simonzhou0372/CHUNITHM_TOF_PICO/src/config.cpp

/*
 * Configuration Implementation
 *
 * 修复说明:
 * 1. 增加 config_init() 启动时的详细日志
 * 2. 增加 config_save() 返回 bool 表示成功/失败
 * 3. 增加 Flash 加载后的参数验证日志
 * 4. 保持与现有代码的兼容性
 */

#include "config.h"
#include "save.h"
#include "mpr121.h"  // 引入 MPR121 默认阈值定义
#include <string.h>
#include <stdio.h>
// 注意: log_output.h 必须在所有 SDK/系统头之后 (见 mpr121.cpp 同名注释)
#include "log_output.h"   // printf 总开关 (默认禁用, 只发送 HID 报文)

namespace Chuni245Tof {

//==============================================================================
// 默认配置
//==============================================================================

// Default configuration - Keyboard mode only
static const config_t default_config = {
    .hid_mode = HID_MODE_KEYBOARD_ONLY,  // Default: Keyboard only
    .touch_threshold = MPR121_DEFAULT_TOUCH_THRESHOLD,      // 由 mpr121.h 定义
    .release_threshold = MPR121_DEFAULT_RELEASE_THRESHOLD,  // 由 mpr121.h 定义
    .tof_offset = 120,                    // Default: 120mm 起始高度
    .tof_pitch = 30,                      // Default: 30mm step height for AIR1~AIR11
    .air12_range = 150,                   // Default: 150mm range for AIR12 (更大的范围)
    .air_min_hold_ms = 100,               // Default: 100ms 最小按下持续时间
    .air_overlay_enabled = 1,             // Default: Overlay ON (扩展到 AIR12)
    .air_threshold = {1500, 1500, 1500, 1500, 1500},
};

//==============================================================================
// 全局配置数据
//==============================================================================

config_t* cfg = nullptr;
static config_t config_data;

// Barrier mode (determined at startup, affects default thresholds)
static uint8_t current_barrier_mode = 2;  // Default: mode 2

//==============================================================================
// 配置验证
//==============================================================================

/**
 * 验证配置参数范围
 * @param cfg 配置指针
 * @return 是否需要修正
 */
static bool validate_config(config_t* cfg) {
    bool modified = false;

    // HID 模式验证
    if (cfg->hid_mode > HID_MODE_GAMEPAD_KEYBOARD) {
        printf("CONFIG VALIDATE: hid_mode %d -> %d (invalid)\r\n",
               cfg->hid_mode, default_config.hid_mode);
        cfg->hid_mode = default_config.hid_mode;
        modified = true;
    }

    // MPR121 阈值范围: 已解除限制，允许调试
    // touch_threshold 和 release_threshold 的合理范围需要用户自行把握
    // 注意：touch_threshold 必须大于 release_threshold（迟滞区）
    if (cfg->touch_threshold < 1 || cfg->touch_threshold > 255) {
        printf("CONFIG VALIDATE: touch_threshold %d -> %d (out of range 1-255)\r\n",
               cfg->touch_threshold, default_config.touch_threshold);
        cfg->touch_threshold = default_config.touch_threshold;
        modified = true;
    }
    if (cfg->release_threshold < 1 || cfg->release_threshold > 255) {
        printf("CONFIG VALIDATE: release_threshold %d -> %d (out of range 1-255)\r\n",
               cfg->release_threshold, default_config.release_threshold);
        cfg->release_threshold = default_config.release_threshold;
        modified = true;
    }

    // TOF 参数验证
    if (cfg->tof_offset < 40 || cfg->tof_offset > 200) {
        printf("CONFIG VALIDATE: tof_offset %d -> %d (out of range 40-200)\r\n",
               cfg->tof_offset, default_config.tof_offset);
        cfg->tof_offset = default_config.tof_offset;
        modified = true;
    }
    if (cfg->tof_pitch < 4 || cfg->tof_pitch > 100) {
        printf("CONFIG VALIDATE: tof_pitch %d -> %d (out of range 4-100)\r\n",
               cfg->tof_pitch, default_config.tof_pitch);
        cfg->tof_pitch = default_config.tof_pitch;
        modified = true;
    }

    // Air12 范围验证：必须 >= pitch
    if (cfg->air12_range < cfg->tof_pitch || cfg->air12_range > 255) {
        printf("CONFIG VALIDATE: air12_range %d -> %d (must be >= pitch %d and <= 255)\r\n",
               cfg->air12_range, default_config.air12_range, cfg->tof_pitch);
        cfg->air12_range = default_config.air12_range;
        modified = true;
    }

    // AIR 最小按下时间验证：10-500ms
    if (cfg->air_min_hold_ms < 10 || cfg->air_min_hold_ms > 500) {
        printf("CONFIG VALIDATE: air_min_hold_ms %d -> %d (out of range 10-500)\r\n",
               cfg->air_min_hold_ms, default_config.air_min_hold_ms);
        cfg->air_min_hold_ms = default_config.air_min_hold_ms;
        modified = true;
    }

    // AIR Overlay 模式验证: 0 或 1
    if (cfg->air_overlay_enabled > 1) {
        printf("CONFIG VALIDATE: air_overlay_enabled %d -> %d (invalid, must be 0 or 1)\r\n",
               cfg->air_overlay_enabled, default_config.air_overlay_enabled);
        cfg->air_overlay_enabled = default_config.air_overlay_enabled;
        modified = true;
    }

    return modified;
}

//==============================================================================
// API 实现
//==============================================================================

/**
 * 设置 barrier mode (在 main.cpp 启动时调用)
 * 影响默认 touch/release 阈值
 */
void config_set_barrier_mode(uint8_t mode) {
    current_barrier_mode = mode;
    printf("CONFIG: Barrier mode set to %d\n", mode);
}

/**
 * 获取当前 barrier mode
 */
uint8_t config_get_barrier_mode() {
    return current_barrier_mode;
}

/**
 * 根据 barrier mode 获取默认 touch 阈值
 */
static uint8_t get_default_touch_threshold() {
    switch (current_barrier_mode) {
        case 0: return 20;  // Mode 0: Direct contact
        case 1: return 3;   // Mode 1: Object barrier
        case 2: return 3;   // Mode 2: Object barrier + glove
        default: return 20;
    }
}

/**
 * 根据 barrier mode 获取默认 release 阈值
 */
static uint8_t get_default_release_threshold() {
    switch (current_barrier_mode) {
        case 0: return 18;  // Mode 0: Direct contact
        case 1: return 2;   // Mode 1: Object barrier
        case 2: return 2;   // Mode 2: Object barrier + glove
        default: return 18;
    }
}

/**
 * 初始化配置
 *
 * 流程:
 * 1. 尝试从 Flash 加载
 * 2. 如果加载失败，使用默认配置
 * 3. 验证参数范围
 * 4. 设置全局指针
 */
void config_init() {
    printf("\r\n========================================\r\n");
    printf("CONFIG INIT: Starting configuration load\r\n");
    printf("========================================\r\n");

    // 尝试从 Flash 加载
    bool loaded = save_load(&config_data, sizeof(config_data));

    if (loaded) {
        printf("CONFIG INIT: Loaded from Flash, validating...\r\n");

        // 验证参数范围
        bool modified = validate_config(&config_data);

        if (modified) {
            printf("CONFIG INIT: Parameters corrected after validation\r\n");
        }

        printf("CONFIG LOAD FLASH: touch=%d release=%d offset=%d pitch=%d air12=%d hold=%d overlay=%d\r\n",
               config_data.touch_threshold, config_data.release_threshold,
               config_data.tof_offset, config_data.tof_pitch,
               config_data.air12_range, config_data.air_min_hold_ms, config_data.air_overlay_enabled);
    } else {
        printf("CONFIG INIT: Flash load failed, using defaults\r\n");
        memcpy(&config_data, &default_config, sizeof(config_data));

        // 根据 runtime barrier mode 设置默认阈值
        config_data.touch_threshold = get_default_touch_threshold();
        config_data.release_threshold = get_default_release_threshold();

        printf("CONFIG LOAD DEFAULT: touch=%d release=%d offset=%d pitch=%d air12=%d hold=%d overlay=%d\r\n",
               config_data.touch_threshold, config_data.release_threshold,
               config_data.tof_offset, config_data.tof_pitch,
               config_data.air12_range, config_data.air_min_hold_ms, config_data.air_overlay_enabled);
    }

    // 设置全局指针
    cfg = &config_data;

    printf("========================================\r\n\r\n");
}

/**
 * 保存当前配置到 Flash
 *
 * @return true 保存成功, false 失败
 */
bool config_save() {
    if (!cfg) {
        printf("CONFIG SAVE: ERROR - config not initialized\r\n");
        return false;
    }

    printf("CONFIG SAVE: Saving current config to Flash...\r\n");
    printf("CONFIG SAVE: touch=%d release=%d offset=%d pitch=%d air12=%d hold=%d overlay=%d\r\n",
           cfg->touch_threshold, cfg->release_threshold,
           cfg->tof_offset, cfg->tof_pitch,
           cfg->air12_range, cfg->air_min_hold_ms, cfg->air_overlay_enabled);

    // 延迟保存: 快照后由 save_loop() 在主循环独立节拍执行 Flash 擦写,
    // 避免 CDC 命令路径直接擦写 Flash 造成实时 HID 长时间停顿
    bool success = save_request_write(cfg, sizeof(config_t));

    if (success) {
        printf("CONFIG SAVE: QUEUED (executes on next main loop)\r\n");
    } else {
        printf("CONFIG SAVE: FAILED to queue\r\n");
    }

    return success;
}

/**
 * 重置配置为默认值并保存
 */
void config_reset() {
    if (!cfg) {
        printf("CONFIG RESET: ERROR - config not initialized\r\n");
        return;
    }

    printf("CONFIG RESET: Resetting to defaults...\r\n");
    memcpy(cfg, &default_config, sizeof(config_t));

    if (config_save()) {
        printf("CONFIG RESET: SUCCESS\r\n");
    } else {
        printf("CONFIG RESET: FAILED to save\r\n");
    }
}

} // namespace Chuni245Tof
