simonzhou0372/CHUNITHM_TOF_PICO/src/save.cpp

/*
 * Flash Save Implementation
 *
 * 修复说明:
 * 1. 修正 Flash 地址计算 - 使用 PICO_FLASH_SIZE_BYTES 而不是硬编码 256KB
 * 2. 增加 CRC32 校验确保数据完整性
 * 3. 增加版本号支持未来配置结构变更
 * 4. 增加写入后验证确保数据正确保存
 * 5. 增加详细的调试日志
 */

#include "save.h"
#include "tof_reader.h"
#include "hardware/flash.h"
#include "pico/mutex.h"
#include "pico/time.h"
#include "pico/flash.h"     // flash_safe_execute: SDK 官方双核 Flash 安全机制
#include <string.h>
#include <stdio.h>
// 注意: log_output.h 必须在所有 SDK/系统头之后 (见 mpr121.cpp 同名注释)
#include "log_output.h"     // printf 总开关 (默认禁用, 只发送 HID 报文)

namespace Chuni245Tof {

//==============================================================================
// Flash 配置
//==============================================================================

// 使用 Flash 最后一个 sector 用于存储配置
// RP2040 Pico 默认 Flash 大小为 2MB (PICO_FLASH_SIZE_BYTES)
// 确保不覆盖程序代码区域
#define CONFIG_FLASH_OFFSET (PICO_FLASH_SIZE_BYTES - FLASH_SECTOR_SIZE)
#define CONFIG_FLASH_ADDR (XIP_BASE + CONFIG_FLASH_OFFSET)

// 配置版本号 - 如果将来 config_t 结构改变，需要增加版本号
#define CONFIG_VERSION 1

//==============================================================================
// 持久化配置结构 (写入 Flash 的格式)
//==============================================================================

typedef struct {
    uint32_t magic;        // Magic number 验证
    uint16_t version;      // 配置版本号
    uint16_t reserved;     // 保留字段（对齐）

    // 配置数据（与 config_t 结构一致）
    uint8_t hid_mode;
    uint8_t touch_threshold;
    uint8_t release_threshold;
    uint8_t tof_offset;
    uint8_t tof_pitch;
    uint8_t air12_range;         // AIR12 特殊检测范围（原 air6_range）
    uint16_t air_min_hold_ms;
    uint8_t air_overlay_enabled; // AIR Overlay Mode (0=OFF, 1=ON)
    uint16_t air_threshold[5];

    uint32_t crc32;        // CRC32 校验
} PersistentConfig;

// 确保结构体大小是 Flash Page 大小的整数倍或更小
static_assert(sizeof(PersistentConfig) <= FLASH_PAGE_SIZE,
              "PersistentConfig too large for Flash page");

//==============================================================================
// CRC32 计算
//==============================================================================

// CRC32 查找表 (IEEE 802.3 标准多项式)
static const uint32_t crc32_table[256] = {
    0x00000000, 0x77073096, 0xEE0E612C, 0x990951BA, 0x076DC419, 0x706AF48F,
    0xE963A535, 0x9E6495A3, 0x0EDB8832, 0x79DCB8A4, 0xE0D5E91E, 0x97D2D988,
    0x09B64C2B, 0x7EB17CBD, 0xE7B82D07, 0x90BF1D91, 0x1DBAD10D, 0x6CABE844,
    0xF856B086, 0x8A1D1A5E, 0xE4D65E39, 0x97D2D9D8, 0x05B6B4A1, 0x7A4D3D6C,
    0x04DB2615, 0x73DC1683, 0xE3630B12, 0x94643B84, 0x0D6D6A3E, 0x7A6A5AA8,
    0xE40ECF0B, 0x9309FF9D, 0x0A00AE27, 0x7D079EB1, 0xF00F9344, 0x8708A3D2,
    0x1E01F268, 0x6906C2FE, 0xF762575D, 0x806567CB, 0x196C3671, 0x6E6B06E7,
    0xFED41B76, 0x89D32BE0, 0x10DA7A5A, 0x67DD4ACC, 0xF9B9DF4F, 0x8EBEEFF9,
    0x17B7BE43, 0x60B08ED5, 0xD6D6A3E8, 0xA1D1937E, 0x38D8C2C4, 0x4FDFF252,
    0xD1BB67F1, 0xA6BC5767, 0x3FB506DD, 0x48B2364B, 0xD80D2BDA, 0xAF0A1B4C,
    0x36034AF6, 0x41047A60, 0xDF60EFC3, 0xA867DF55, 0x316E8EEF, 0x4669BE79,
    0xCB61B38C, 0xBC66831A, 0x256FD2A0, 0x5268E236, 0xCC0C7795, 0xBB0B4703,
    0x220216B9, 0x5505262F, 0xC5BA3BBE, 0xB2BD0B28, 0x2BB45A92, 0x5CB36A04,
    0xC2D7FFA7, 0xB5D0CF31, 0x2CD99E8B, 0x5BDEAE1D, 0x9B64C2B0, 0xEC63F22A,
    0x756AA39C, 0x026D930A, 0x9C0906A9, 0xEB0E363F, 0x72076785, 0x05005713,
    0x95BF4A82, 0xE2B87A14, 0x7BB12BAE, 0x0CB61B38, 0x92D28E9B, 0xE5D5BE41,
    0x7CDCEFB7, 0x0BDBDF21, 0x86D0D2D4, 0xF1C4E242, 0x68DDB3F8, 0x1FDA836E,
    0x81BE16CD, 0xF6B9265B, 0x6FB077E1, 0x18B74777, 0x88085AE6, 0xFF0F6A70,
    0x66063BCA, 0x11010B5C, 0x8F659EFF, 0xF862AE69, 0x616BFFD3, 0x166CCF45,
    0xA00AE278, 0xD70DD2EE, 0x4E048354, 0x3903B3C2, 0xA7672661, 0xD06016F7,
    0x4969474D, 0x3E6E77DB, 0xAED16A4A, 0xD9D65ADC, 0x40DF0B66, 0x37D83BF0,
    0xA9BCAE53, 0xDEBB9EC5, 0x47B2CF7F, 0x30B5FFE9, 0xBDBDF21C, 0xCABAC28A,
    0x53B39330, 0x24B4A3A6, 0xBAD03605, 0xCDD70693, 0x54DE5729, 0x23D967BF,
    0xB3667A2E, 0xC4614AB8, 0x5D681B02, 0x2A6F2B94, 0xB40BBE37, 0xC31C666A,
    0x5B2F6D36, 0x2CD4F1B8, 0x4B91349A, 0x38C26AB0, 0x5CC7A4B2, 0x2BD5AF96,
    0x4399AE78, 0x3A8BE6B8, 0x58D4B97A, 0x28C4E57C, 0x4C3DD7D8, 0x3A39D274,
    0x5A8F93D0, 0x2A7F9F5E, 0x4C39DB76, 0x3A2DC14E, 0x5AD0CE9C, 0x2AD7DBD2,
    0x4C456158, 0x3A3A7528, 0x5B3BCC56, 0x2B3436A8, 0x4C6E1D82, 0x3A4D65F4,
    0x5B7A8F1E, 0x2B82C870, 0x4C98474C, 0x3A98C758, 0x5BDF2A3C, 0x2BECAB18,
    0x4CF0E79E, 0x3AED66D0, 0x5C3F7A8C, 0x2C832B94, 0x4D00F694, 0x3AFE2970,
    0x5C594E28, 0x2CF02B30, 0x4D34AB04, 0x3B28BBD0, 0x5C93CCDC, 0x2D02EF8D
};

/**
 * 计算 CRC32
 * @param data 数据指针
 * @param len 数据长度
 * @return CRC32 值
 */
static uint32_t calculate_crc32(const uint8_t* data, uint32_t len) {
    uint32_t crc = 0xFFFFFFFF;
    for (uint32_t i = 0; i < len; i++) {
        uint8_t index = (crc ^ data[i]) & 0xFF;
        crc = (crc >> 8) ^ crc32_table[index];
    }
    return crc ^ 0xFFFFFFFF;
}

//==============================================================================
// 模块状态
//==============================================================================

static mutex_t* save_mutex = nullptr;
static uint32_t save_magic = 0;
static bool save_initialized = false;

// 延迟保存请求（仅 Core0 访问）
static uint8_t pending_data[FLASH_PAGE_SIZE];
static uint32_t pending_len = 0;
static volatile bool pending_flag = false;
static uint64_t first_pending_us = 0;   // 最早一次 pending 的时刻 (空闲门控超时用)

// 空闲窗口门控: SAVE 只在 "无按键活动" 或 "等待超过上限" 时执行,
// 避免游戏运行中随机出现一次 USB 短暂停
static volatile bool idle_hint = true;
static const uint32_t SAVE_FORCE_DELAY_MS = 10000;

// 执行统计 (RAM 常驻, 可经 STATUS 读取)
static uint32_t save_count = 0;
static uint32_t save_fail_count = 0;
static uint32_t max_save_duration_us = 0;
static uint64_t last_save_start_us = 0;
static uint64_t last_save_end_us = 0;

// flash_safe_execute 参数包
typedef struct {
    uint32_t offset;
    const uint8_t* data;
    size_t size;
    bool done;
} flash_op_t;

// flash_safe_execute 回调: 在双核安全 + 中断关闭的上下文中执行,
// 只做纯 Flash 擦写, 不触碰任何外设/USB/I2C
static void flash_erase_program_cb(void* p) {
    flash_op_t* op = (flash_op_t*)p;
    flash_range_erase(op->offset, FLASH_SECTOR_SIZE);
    flash_range_program(op->offset, op->data, op->size);
    op->done = true;
}

// 主循环每轮更新空闲提示: 无任何按键活动 = true
void save_set_idle_hint(bool idle) {
    idle_hint = idle;
}

//==============================================================================
// API 实现
//==============================================================================

void save_init(uint32_t magic, mutex_t* mutex) {
    save_magic = magic;
    save_mutex = mutex;
    save_initialized = true;

    printf("CONFIG FLASH: Offset=0x%X, Addr=0x%X, SectorSize=%d, PageSize=%d\r\n",
           CONFIG_FLASH_OFFSET, CONFIG_FLASH_ADDR, FLASH_SECTOR_SIZE, FLASH_PAGE_SIZE);
}

/**
 * 从 Flash 加载配置
 *
 * 验证步骤:
 * 1. Magic number
 * 2. Version
 * 3. CRC32
 * 4. 参数范围合法性
 *
 * @param data 输出缓冲区
 * @param len 数据长度
 * @return true 加载成功, false 失败(使用默认配置)
 */
bool save_load(void* data, uint32_t len) {
    if (!save_initialized || !data) {
        printf("CONFIG LOAD: ERROR - not initialized or null data\r\n");
        return false;
    }

    const PersistentConfig* flash_cfg = (const PersistentConfig*)CONFIG_FLASH_ADDR;

    // 1. 验证 Magic Number
    if (flash_cfg->magic != save_magic) {
        printf("CONFIG LOAD: Magic mismatch (expected 0x%08X, got 0x%08X), using defaults\r\n",
               save_magic, flash_cfg->magic);
        return false;
    }

    // 2. 验证版本号
    if (flash_cfg->version > CONFIG_VERSION) {
        printf("CONFIG LOAD: Version mismatch (expected <= %d, got %d), using defaults\r\n",
               CONFIG_VERSION, flash_cfg->version);
        return false;
    }

    // 3. 验证 CRC32
    // 计算从 magic 到 crc32 字段之前的所有数据的 CRC
    uint32_t calc_crc = calculate_crc32((const uint8_t*)flash_cfg,
                                         offsetof(PersistentConfig, crc32));
    if (flash_cfg->crc32 != calc_crc) {
        printf("CONFIG LOAD: CRC mismatch (expected 0x%08X, got 0x%08X), using defaults\r\n",
               calc_crc, flash_cfg->crc32);
        return false;
    }

    // 4. 复制数据到输出缓冲区 (只复制 config_t 部分)
    // 注意: config.cpp 传入的 len 是 sizeof(config_t)
    // 我们需要正确映射字段

    // 从 PersistentConfig 提取数据到 config_t
    // 这里假设 config_t 的字段顺序与 PersistentConfig 一致
    // 更安全的方法是逐字段复制

    // 简单的内存复制 (保持与原始实现的兼容性)
    // config_t 结构在 config.h 中定义
    uint8_t* dest = (uint8_t*)data;

    // 复制配置字段 (从 hid_mode 开始)
    memcpy(dest, &flash_cfg->hid_mode, len);

    printf("CONFIG LOAD: SUCCESS from Flash (magic=0x%08X, version=%d)\r\n",
           flash_cfg->magic, flash_cfg->version);

    return true;
}

/**
 * 保存配置到 Flash
 *
 * 步骤:
 * 1. 准备 PersistentConfig 结构
 * 2. 计算 CRC32
 * 3. 擦除 Flash sector
 * 4. 写入 Flash
 * 5. 读回验证
 *
 * @param data 配置数据指针
 * @param len 数据长度
 * @return true 保存成功, false 失败
 */
bool save_write(const void* data, uint32_t len) {
    if (!save_initialized || !data) {
        printf("CONFIG SAVE: ERROR - not initialized or null data\r\n");
        return false;
    }

    // ★ 不再加锁 (旧实现 mutex_enter_blocking 是无界阻塞等待)。
    //   本函数只在 Core0 主循环的 save_loop() 空闲窗口被调用, Core1
    //   从不触碰 save 模块 (I2C1/VL53L0X 与 Flash 保存无共享状态),
    //   单写者模型下互斥锁是多余的 —— 且它是 "USB+LED 同时停摆" 的
    //   候选阻塞源之一: 若锁被占, mutex_enter_blocking 无限期自旋。

    printf("CONFIG SAVE: Starting save operation...\r\n");

    // 1. 准备 PersistentConfig 结构
    PersistentConfig cfg_to_save;
    memset(&cfg_to_save, 0, sizeof(cfg_to_save));

    cfg_to_save.magic = save_magic;
    cfg_to_save.version = CONFIG_VERSION;
    cfg_to_save.reserved = 0;

    // 复制配置数据 (从 config_t 到 PersistentConfig)
    // 假设 data 指向 config_t 结构
    const uint8_t* src = (const uint8_t*)data;
    memcpy(&cfg_to_save.hid_mode, src, len);

    // 2. 计算 CRC32 (计算从 magic 到 crc32 字段之前)
    cfg_to_save.crc32 = calculate_crc32((const uint8_t*)&cfg_to_save,
                                         offsetof(PersistentConfig, crc32));

    printf("CONFIG SAVE: Magic=0x%08X, Version=%d, CRC=0x%08X\r\n",
           cfg_to_save.magic, cfg_to_save.version, cfg_to_save.crc32);

    // 3. 准备写入缓冲区 (必须对齐到 FLASH_PAGE_SIZE)
    uint8_t buffer[FLASH_PAGE_SIZE];
    memset(buffer, 0xFF, sizeof(buffer));  // Flash erase 后是 0xFF
    memcpy(buffer, &cfg_to_save, sizeof(cfg_to_save));

    // 4. 擦除和写入 Flash
    // 使用 SDK 官方 flash_safe_execute (pico_flash) —— 它内部负责
    // multicore lockout (Core1 已在启动时调用 flash_safe_execute_core_init()
    // 注册为 victim) + 中断关闭, 是双核 + XIP 环境下擦写 Flash 的官方安全机制。
    // 注意: 擦写期间 USB 仍会暂停 (XIP 停摆, 典型 ~50ms, 最坏 ~400ms, 硬件
    // 层面不可避免), 因此 SAVE 被设计为延迟 + 择机执行 (见 save_loop),
    // 绝不在实时路径随机触发; 擦写本身只在 RAM 执行的回调中进行。
    flash_op_t op = {
        .offset = CONFIG_FLASH_OFFSET,
        .data = buffer,
        .size = FLASH_PAGE_SIZE,
        .done = false,
    };
    // A stopped Core1 must not hold Core0 for 1s entry + 1s exit, which can
    // exceed the 2s watchdog once flash erase time is included.
    if (!tof_reader_flash_ready() || tof_reader_get_progress_age_us() > 10000) {
        save_fail_count++;
        return false;
    }
    int rc = flash_safe_execute(flash_erase_program_cb, &op, 10);

    if (rc != PICO_ERROR_NONE || !op.done) {
        // 超时/双核协作失败: 放弃本次写入, 不重试 (Flash 异常属硬件级,
        // 自动重试风险更大)
        printf("CONFIG SAVE: flash_safe_execute failed rc=%d\r\n", rc);
        save_fail_count++;
        return false;
    }

    // 5. 读回验证
    printf("CONFIG SAVE: Verifying write...\r\n");

    const PersistentConfig* flash_cfg = (const PersistentConfig*)CONFIG_FLASH_ADDR;

    // 验证 magic
    if (flash_cfg->magic != cfg_to_save.magic) {
        printf("CONFIG SAVE: VERIFY FAILED - Magic mismatch (wrote 0x%08X, read 0x%08X)\r\n",
               cfg_to_save.magic, flash_cfg->magic);
        return false;
    }

    // 验证版本
    if (flash_cfg->version != cfg_to_save.version) {
        printf("CONFIG SAVE: VERIFY FAILED - Version mismatch (wrote %d, read %d)\r\n",
               cfg_to_save.version, flash_cfg->version);
        return false;
    }

    // 验证 CRC
    if (flash_cfg->crc32 != cfg_to_save.crc32) {
        printf("CONFIG SAVE: VERIFY FAILED - CRC mismatch (wrote 0x%08X, read 0x%08X)\r\n",
               cfg_to_save.crc32, flash_cfg->crc32);
        return false;
    }

    // 验证数据内容
    if (memcmp(&flash_cfg->hid_mode, &cfg_to_save.hid_mode, len) != 0) {
        printf("CONFIG SAVE: VERIFY FAILED - Data mismatch\r\n");
        return false;
    }

    printf("CONFIG SAVE: SUCCESS - Verified magic, version, CRC, and data\r\n");

    return true;
}

// 请求保存（延迟执行）: 立即快照配置, 实际 Flash 擦写交给 save_loop()
bool save_request_write(const void* data, uint32_t len) {
    if (!save_initialized || !data) {
        printf("CONFIG SAVE: ERROR - not initialized or null data\r\n");
        return false;
    }
    if (len > sizeof(PersistentConfig)) {
        printf("CONFIG SAVE: ERROR - len %u too large\r\n", (unsigned)len);
        return false;
    }
    if (pending_flag) {
        printf("CONFIG SAVE: ERROR - another save already pending\r\n");
        return false;
    }

    // 立即快照: Flash 写入使用请求时刻的一致性数据
    memcpy(pending_data, data, len);
    pending_len = len;
    pending_flag = true;
    first_pending_us = 0;   // 空闲门控计时从下一次 save_loop 开始
    return true;
}

bool save_pending() {
    return pending_flag;
}

// Core0 主循环低优先级调用: 执行待保存的 Flash 擦写。
// 注意: 擦写期间 USB 约 50-400ms 无输出 (双核 XIP 停摆, 硬件层面不可避免),
// 因此绝不从 CDC 命令解析路径同步调用, 而是延迟到主循环的独立节拍执行;
// 且只在 "无按键活动" (空闲窗口) 或等待超过 SAVE_FORCE_DELAY_MS 时执行,
// 保证这个受控的 USB 短暂停绝不随机落在游戏进行中。
void save_loop() {
    if (!pending_flag) return;

    // 空闲窗口门控: 有按键活动时不执行 (除非等待超过上限, 防止永不提交)
    // Require continuous idle; never force a save while keys are active.
    if (!idle_hint) { first_pending_us = 0; return; }
    const uint64_t now = time_us_64();
    if (!first_pending_us) first_pending_us = now;
    if (now - first_pending_us < 2000000) return;
    first_pending_us = 0;

    pending_flag = false;

    printf("CONFIG SAVE: deferred flash write starting (USB pauses briefly)...\r\n");

    last_save_start_us = time_us_64();
    bool ok = save_write(pending_data, pending_len);
    last_save_end_us = time_us_64();

    uint32_t dur_us = (uint32_t)(last_save_end_us - last_save_start_us);
    if (dur_us > max_save_duration_us) max_save_duration_us = dur_us;

    if (ok) {
        save_count++;
    } else {
        save_fail_count++;
    }

    printf(ok ? "SAVE OK\r\n" : "SAVE ERROR\r\n");
}

// 供 STATUS/PERF 输出的执行统计
uint32_t save_get_count(void)           { return save_count; }
uint32_t save_get_fail_count(void)      { return save_fail_count; }
uint32_t save_get_max_duration_us(void) { return max_save_duration_us; }
uint64_t save_get_last_start_us(void)   { return last_save_start_us; }
uint64_t save_get_last_end_us(void)     { return last_save_end_us; }

} // namespace Chuni245Tof
