simonzhou0372/CHUNITHM_TOF_PICO/src/air.h

/*
 * Air Sensor Header
 *
 * 改进：
 * - 使用滞回机制避免边界抖动
 * - 使用真实的 TOF 数据时间戳
 * - 支持数据有效性检查
 */

#ifndef AIR_H
#define AIR_H

#include <stdint.h>
#include <stdbool.h>

namespace Chuni245Tof {

void air_init();
void air_update();
uint8_t air_get_bitmap();      // 返回 HID 输出状态 (6-bit: key1~key6)
uint16_t air_get_air_state();  // 返回完整 AIR 状态 (12-bit: AIR1~AIR12)
bool air_is_triggered(uint8_t sensor);
uint16_t air_get_distance(uint8_t sensor);

// 设置阈值（保留接口）
void air_set_threshold(uint8_t sensor, uint16_t threshold_mm);

// 获取调试数据
typedef struct {
    uint16_t max_distance;        // 当前最大距离 (仅用于调试，不参与 AIR 判定)
    uint16_t sensor_bitmap;       // AIR 状态 (12-bit: AIR1~AIR12)
    uint8_t hid_bitmap;           // HID 输出状态 (6-bit: key1~key6)
    uint32_t timestamp_us;        // 更新时间戳
    uint16_t sensor_distances[5]; // 各传感器距离
    uint32_t sensor_ages[5];      // 各传感器数据年龄
    bool sensor_valid[5];         // 各传感器数据有效性
    uint8_t sensor_air_layer[5];  // 各传感器当前 AIR layer (0~11 = AIR1~AIR12, 0xFF = 无效)
} air_debug_data_t;

air_debug_data_t air_get_debug_data();

} // namespace Chuni245Tof

using namespace Chuni245Tof;

#endif /* AIR_H */
